Critters/WiFiAirQualityThing/build photos/img-back.jpg

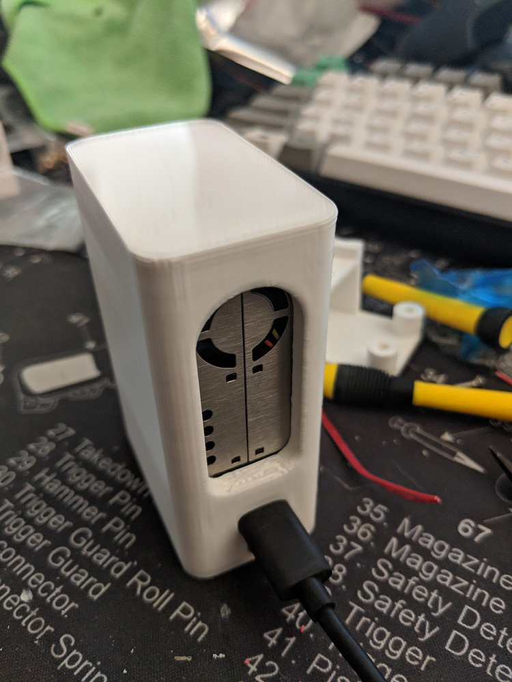
build photos/img-back.jpg
