Critters/WiFiAirQualityThing/build photos/img-scale.jpg

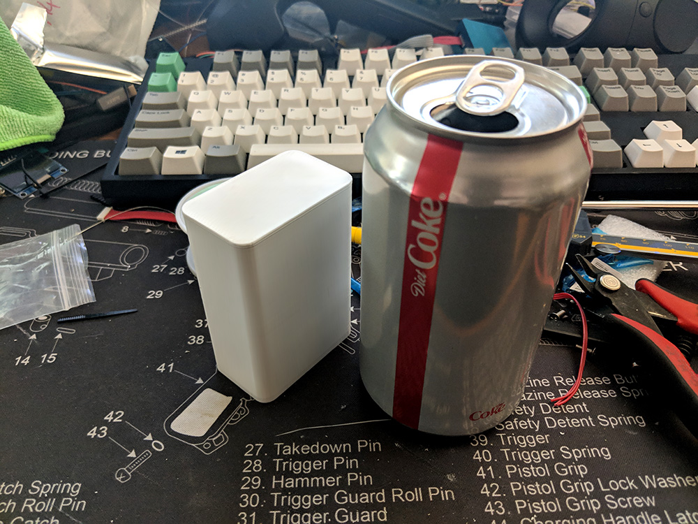
build photos/img-scale.jpg
